slugrustle/electronics/Big_Fast_Switch/Simulation/Diode_SPICE_Models.pdf

3.13. OTHER DIODE TECHNOLOGIES | 163

or laser diode’s optimum forward current. This is especially important for the laser diode, not so much for the LED, as regular LEDs tend to be more tolerant of forward current variations. Another application is in the charging of small secondary-cell batteries, where a constant charging current leads to predictable charging times. Of course, large secondary-cell battery banks might also benefit from constant-current charging, but constant-current diodes tend to be very small devices, limited to regulating currents in the milliamp range.

## 3.13 Other diode technologies

### 3.13.1 SiC diodes

Diodes manufactured from silicon carbide are capable of high temperature operation to 400oC. This could be in a high temperature environment: down hole oil well logging, gas turbine engines, auto engines. Or, operation in a moderate environment at high power dissipation. Nuclear and space applications are promising as SiC is 100 times more resistant to radiation compared with silicon. SiC is a better conductor of heat than any metal. Thus, SiC is better than silicon at conducting away heat. Breakdown voltage is several kV. SiC power devices are expected to reduce electrical energy losses in the power industry by a factor of 100.

### 3.13.2 Polymer diode

Diodes based on organic chemicals have been produced using low temperature processes. Hole rich and electron rich conductive polymers may be ink jet printed in layers. Most of the research and development is of the organic LED (OLED). However, development of inexpensive printable organic RFID (radio frequency identification) tags is on going. In this effort, a pentacene organic rectifier has been operated at 50 MHz. Rectification to 800 MHz is a development goal. An inexpensive metal insulator metal (MIM) diode acting like a back-to-back zener diode clipper has been delveloped. Also, a tunnel diode like device has been fabricated.

## 3.14 SPICE models

The SPICE circuit simulation program provides for modeling diodes in circuit simulations. The diode model is based on characterization of individual devices as described in a product data sheet and manufacturing process characteristics not listed. Some information has been extracted from a 1N4004 data sheet in Figure 3.86.
The diode statement begins with a diode element name which must begin with “d” plus optional characters. Example diode element names include: d1, d2, dtest, da, db, d101. Two node numbers specify the connection of the anode and cathode, respectively, to other components. The node numbers are followed by a model name, referring to a subsequent “.model” statement.
The model statement line begins with “.model,” followed by the model name matching one or more diode statements. Next, a “d” indicates a diode is being modeled. The remainder of the model statement is a list of optional diode parameters of the form Parameter-

164 CHAPTER 3. DIODES AND RECTIFIERS

1

10

100

1 | 10 | 100

1.0

10

0.6 | 1.6

0.01

0.1

0.8 1.0 1.2 1.4
VF

instaneous forward voltage (V)

### IF instaneous forward current (I)

VR reverse voltage (V)

### CJ junction capacitance (pF)

30

0.925

Max avg rectified current IO (A) 1 Peak repetitive reverse voltage VRRM (V) 400 Peak forward surge current IFSM (A) 30

Forward voltage drop VF

(V) 1
@ IF
(A) 1
Max reverse current IR (µΑ) 5 Total capacitance CT
(pF) 15 | @ VR (V) 400

Figure 3.86: Data sheet 1N4004 excerpt, after [6].

Name=ParameterValue. None are used in Example below. Example2 has some parameters defined. For a list of diode parameters, see Table 3.6.

General form: d[name] [anode] [cathode] [modelname]
.model ([modelname] d [parmtr1=x] [parmtr2=y] . . .)
Example: | d1 1 2 mod1
.model mod1 d
Example2: | D2 1 2 Da1N4004
.model Da1N4004 D (IS=18.8n RS=0 BV=400 IBV=5.00u CJO=30 M=0.333 N=2)

The easiest approach to take for a SPICE model is the same as for a data sheet: consult the manufacturer’s web site. Table 3.7 lists the model parameters for some selected diodes. A fallback strategy is to build a SPICE model from those parameters listed on the data sheet. A third strategy, not considered here, is to take measurements of an actual device. Then, calculate, compare and adjust the SPICE parameters to the measurements.
If diode parameters are not specified as in “Example” model above, the parameters take on the default values listed in Table 3.6 and Table 3.7. These defaults model integrated circuit diodes. These are certainly adequate for preliminary work with discrete devices For more critical work, use SPICE models supplied by the manufacturer [5], SPICE vendors, and other

3.14. SPICE MODELS | 165

Table 3.6: Diode SPICE parameters
Symbol | Name | Parameter | Units | Default
IS | IS | Saturation current (diode equa-
| | tion)

A 1E-14

RS | RS | Parsitic resistance (series resis-
| | tance) | Ω | 0
n | N | Emission coefficient, 1 to 2 | - | 1
τ D | TT | Transit time | s | 0
CD(0) | CJO | Zero-bias junction capacitance | F | 0
φ0 | VJ | Junction potential | V | 1
m | M | Junction grading coefficient | - | 0.5
- | - | 0.33 for linearly graded junc-
| | tion
- | - | 0.5 for abrupt junction | - | -
Eg | EG | Activation energy: | eV | 1.11
- | - | Si: 1.11 | - | -
- | - | Ge: 0.67 | - | -
- | - | Schottky: 0.69 | - | -
pi | XTI | IS temperature exponent | - | 3.0
- | - | pn junction: 3.0 | - | -
- | - | Schottky: 2.0 | - | -
kf | KF | Flicker noise coefficient | - | 0
af | AF | Flicker noise exponent | - | 1
FC | FC | Forward bias depletion capaci-
| | tance coefficient
- 0.5
BV | BV | Reverse breakdown voltage | V | ∞
IBV | IBV | Reverse breakdown current | A | 1E-3

166 CHAPTER 3. DIODES AND RECTIFIERS

sources. [16]

Table 3.7: SPICE parameters for selected diodes; sk=schottky Ge=germanium; else silicon.
Part | IS | RS | N | TT | CJO | M | VJ | EG | XTI | BV | IBV
Default 1N5711 sk 1N5712 sk 1N34 Ge 1N4148 1N3891 10A04 10A 1N4004 1A 1N4004 data sheet | 1E-14 315n 680p 200p 35p 63n 844n 76.9n 18.8n | 0 2.8 12 84m 64m 9.6m 2.06m 42.2m - | 1 2.03 1.003 2.19 1.24 2 2.06 1.45 2 | 0 1.44n 50p 144n 5.0n 110n 4.32u 4.32u - | 0 2.00p 1.0p 4.82p 4.0p 114p 277p 39.8p 30p | 0.5 0.333 0.5 0.333 0.285 0.255 0.333 0.333 0.333 | 1 -0.6 0.75 0.6 0.6 --- | 1.11 0.69 0.69 0.67 ----- | 3 2 2 ------ | ∞ 70 20 60 75 250 400 400 400 | 1m 10u -15u --10u 5u 5u

Otherwise, derive some of the parameters from the data sheet. First select a value for spice parameter N between 1 and 2. It is required for the diode equation (n). Massobrio [1] pp 9, recommends ”.. n, the emission coefficient is usually about 2.” In Table 3.7, we see that power rectifiers 1N3891 (12 A), and 10A04 (10 A) both use about 2. The first four in the table are not relevant because they are schottky, schottky, germanium, and silicon small signal, respectively. The saturation current, IS, is derived from the diode equation, a value of (VD, ID) on the graph in Figure 3.86, and N=2 (n in the diode equation).

ID = IS(e

VD/nVT − 1)

VT = 26 mV at 25oC | n = 2.0 | VD = 0.925 V at 1 A from graph

1 A = IS(e

(0.925V )/(2)(26mV ) − 1)

IS = 18.8E-9

The numerical values of IS=18.8n and N=2 are entered in last line of Table 3.7 for comparison to the manufacturers model for 1N4004, which is considerably different. RS defaults to 0 for now. It will be estimated later. The important DC static parameters are N, IS, and RS. Rashid [15] suggests that TT, τ D, the transit time, be approximated from the reverse recovery stored charge QRR, a data sheet parameter (not available on our data sheet) and IF , forward current.

ID = IS(e

VD/nVT − 1)

τ D = QRR/IF

We take the TT=0 default for lack of QRR. Though it would be reasonable to take TT for a similar rectifier like the 10A04 at 4.32u. The 1N3891 TT is not a valid choice because it is a

3.14. SPICE MODELS | 167

fast recovery rectifier. CJO, the zero bias junction capacitance is estimated from the VR vs CJ graph in Figure 3.86. The capacitance at the nearest to zero voltage on the graph is 30 pF at 1 V. If simulating high speed transient response, as in switching regulator power supplies, TT and CJO parameters must be provided.
The junction grading coefficient M is related to the doping profile of the junction. This is not a data sheet item. The default is 0.5 for an abrupt junction. We opt for M=0.333 corresponding to a linearly graded junction. The power rectifiers in Table 3.7 use lower values for M than 0.5. We take the default values for VJ and EG. Many more diodes use VJ=0.6 than shown in Table 3.7. However the 10A04 rectifier uses the default, which we use for our 1N4004 model (Da1N4001 in Table 3.6). Use the default EG=1.11 for silicon diodes and rectifiers. Table 3.6 lists values for schottky and germanium diodes. Take the XTI=3, the default IS temperature coefficient for silicon devices. See Table 3.6 for XTI for schottky diodes.
The abbreviated data sheet, Figure 3.86, lists IR = 5 µA @ VR = 400 V, corresponding to IBV=5u and BV=400 respectively. The 1n4004 SPICE parameters derived from the data sheet are listed in the last line of Table 3.7 for comparison to the manufacturer’s model listed above it. BV is only necessary if the simulation exceeds the reverse breakdown voltage of the diode, as is the case for zener diodes. IBV, reverse breakdown current, is frequently omitted, but may be entered if provided with BV.
Figure 3.87 shows a circuit to compare the manufacturers model, the model derived from the datasheet, and the default model using default parameters. The three dummy 0 V sources are necessary for diode current measurement. The 1 V source is swept from 0 to 1.4 V in 0.2 mV steps. See .DC statement in the netlist in Table 3.8. DI1N4004 is the manufacturer’s diode model, Da1N4004 is our derived diode model.

0

+
− 1V

D1 D2 1

0V −

0V −

0V −

D3

Figure 3.87: SPICE circuit for comparison of manufacturer model (D1), calculated datasheet model (D2), and default model (D3).

We compare the three models in Figure 3.88. and to the datasheet graph data in Table 3.9. VD is the diode voltage versus the diode currents for the manufacturer’s model, our calculated datasheet model and the default diode model. The last column “1N4004 graph” is from the datasheet voltage versus current curve in Figure 3.86 which we attempt to match. Comparison of the currents for the three model to the last column shows that the default model is good at low currents, the manufacturer’s model is good at high currents, and our calculated datasheet model is best of all up to 1 A. Agreement is almost perfect at 1 A because the IS calculation is based on diode voltage at 1 A. Our model grossly over states current above 1 A.
The solution is to increase RS from the default RS=0. Changing RS from 0 to 8m in the datasheet model causes the curve to intersect 10 A (not shown) at the same voltage as the manufacturer’s model. Increasing RS to 28.6m shifts the curve further to the right as shown in

168 CHAPTER 3. DIODES AND RECTIFIERS

Table 3.8: SPICE netlist parameters: (D1) DI1N4004 manufacturer’s model, (D2) Da1N40004 datasheet derived, (D3) default diode model.
*SPICE circuit <03468.eps> from XCircuit v3.20
D1 1 5 DI1N4004
V1 5 0 0
D2 1 3 Da1N4004
V2 3 0 0
D3 1 4 Default
V3 4 0 0
V4 1 0 1
.DC V4 0 1400mV 0.2m
.model Da1N4004 D (IS=18.8n RS=0 | BV=400 IBV=5.00u CJO=30
+M=0.333 | N=2.0 TT=0)
.MODEL DI1N4004 D (IS=76.9n RS=42.0m BV=400 IBV=5.00u CJO=39.8p +M=0.333 N=1.45 TT=4.32u)
.MODEL Default D
.end

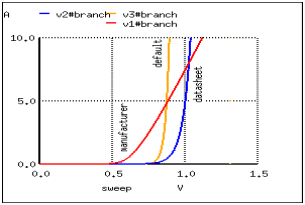
[picture p3: figure]

Figure 3.88: First trial of manufacturer model, calculated datasheet model, and default model.

3.14. SPICE MODELS | 169

Table 3.9: Comparison of manufacturer model, calculated datasheet model, and default model to 1N4004 datasheet graph of V vs I.

| | model | model | model
1N4004
index | VD | manufacturer | datasheet | default
graph
3500 | 7.000000e-01 | 1.612924e+00 | 1.416211e-02 | 5.674683e-03
0.01
4001 | 8.002000e-01 | 3.346832e+00 | 9.825960e-02 | 2.731709e-01
0.13
4500 | 9.000000e-01 | 5.310740e+00 | 6.764928e-01 | 1.294824e+01
0.7
4625 | 9.250000e-01 | 5.823654e+00 | 1.096870e+00 | 3.404037e+01
1.0
5000 | 1.000000e-00 | 7.395953e+00 | 4.675526e+00 | 6.185078e+02
2.0
5500 | 1.100000e+00 | 9.548779e+00 | 3.231452e+01 | 2.954471e+04
3.3
6000 | 1.200000e+00 | 1.174489e+01 | 2.233392e+02 | 1.411283e+06
5.3
6500 | 1.300000e+00 | 1.397087e+01 | 1.543591e+03 | 6.741379e+07
8.0
7000 | 1.400000e+00 | 1.621861e+01 | 1.066840e+04 | 3.220203e+09 12.

170 CHAPTER 3. DIODES AND RECTIFIERS

Figure 3.89. This has the effect of more closely matching our datasheet model to the datasheet graph (Figure 3.86). Table 3.10 shows that the current 1.224470e+01 A at 1.4 V matches the graph at 12 A. However, the current at 0.925 V has degraded from 1.096870e+00 above to 7.318536e-01.

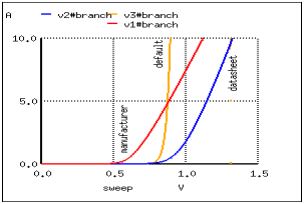
[picture p4: figure]

Figure 3.89: Second trial to improve calculated datasheet model compared with manufacturer model and default model.

Table 3.10: Changing Da1N4004 model statement RS=0 to RS=28.6m decreases the current at VD=1.4 V to 12.2 A.
.model Da1N4004 D (IS=18.8n RS=28.6m BV=400 IBV=5.00u CJO=30
+M=0.333 | N=2.0 TT=0)
| | model | model | 1N4001
index | VD | manufacturer | datasheet | graph
3505 | 7.010000e-01 | 1.628276e+00 | 1.432463e-02 | 0.01
4000 | 8.000000e-01 | 3.343072e+00 | 9.297594e-02 | 0.13
4500 | 9.000000e-01 | 5.310740e+00 | 5.102139e-01 | 0.7
4625 | 9.250000e-01 | 5.823654e+00 | 7.318536e-01 | 1.0
5000 | 1.000000e-00 | 7.395953e+00 | 1.763520e+00 | 2.0
5500 | 1.100000e+00 | 9.548779e+00 | 3.848553e+00 | 3.3
6000 | 1.200000e+00 | 1.174489e+01 | 6.419621e+00 | 5.3
6500 | 1.300000e+00 | 1.397087e+01 | 9.254581e+00 | 8.0
7000 | 1.400000e+00 | 1.621861e+01 | 1.224470e+01 | 12.

Suggested reader exercise: decrease N so that the current at VD=0.925 V is restored to 1
A. This may increase the current (12.2 A) at VD=1.4 V requiring an increase of RS to decrease current to 12 A.

3.14. SPICE MODELS | 171

Zener diode: There are two approaches to modeling a zener diode: set the BV parameter to the zener voltage in the model statement, or model the zener with a subcircuit containing a diode clamper set to the zener voltage. An example of the first approach sets the breakdown voltage BV to 15 for the 1n4469 15 V zener diode model (IBV optional):

.model D1N4469 D ( BV=15 IBV=17m )

The second approach models the zener with a subcircuit. Clamper D1 and VZ in Figure ?? models the 15 V reverse breakdown voltage of a 1N4477A zener diode. Diode DR accounts for the forward conduction of the zener in the subcircuit.

+

−
13.7 V

1
3

2

A

K

D1

.SUBCKT DI-1N4744A
1 2
* Terminals A K
D1 1 2 DF
DZ 3 1 DR
VZ 2 3 13.7
.MODEL DF D (
IS=27.5p RS=0.620
N=1.10
+ CJO=78.3p
VJ=1.00 M=0.330
TT=50.1n )
.MODEL DR D (
IS=5.49f RS=0.804
N=1.77 )
.ENDS

Figure 3.90: Zener diode subcircuit uses clamper (D1 and VZ) to model zener.

Tunnel diode: A tunnel diode may be modeled by a pair of field effect transistors (JFET) in a SPICE subcircuit. [11] An oscillator circuit is also shown in this reference.
Gunn diode: A Gunn diode may also be modeled by a pair of JFET’s. [12] This reference shows a microwave relaxation oscillator.
- REVIEW:
- Diodes are described in SPICE by a diode component statement referring to .model statement. The .model statement contains parameters describing the diode. If parameters are not provided, the model takes on default values.
- Static DC parameters include N, IS, and RS. Reverse breakdown parameters: BV, IBV.
- Accurate dynamic timing requires TT and CJO parameters
- Models provided by the manufacturer are highly recommended.
