slugrustle/electronics/Big_Fast_Switch/MOSFET_and_NTC_Heatsink_Mounting.jpg

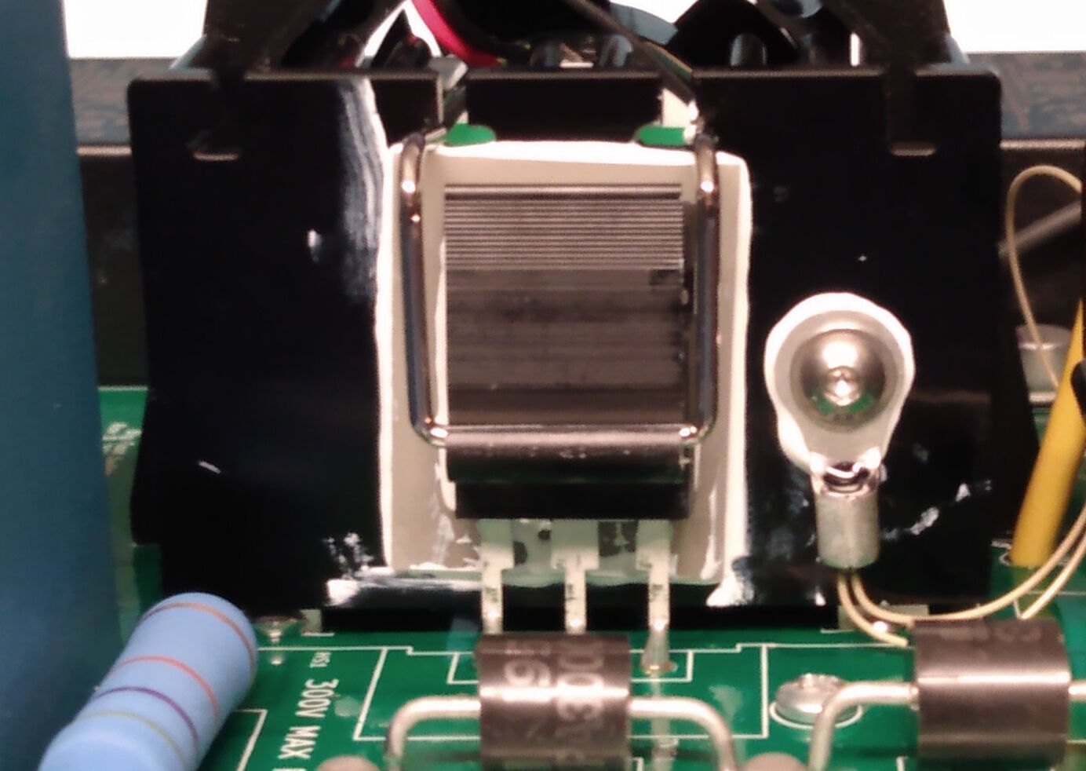
Big_Fast_Switch/MOSFET_and_NTC_Heatsink_Mounting.jpg
