slugrustle/electronics/HighImpedanceBuffer/Enclosure/BufferBoxLid_DiagonalView.png

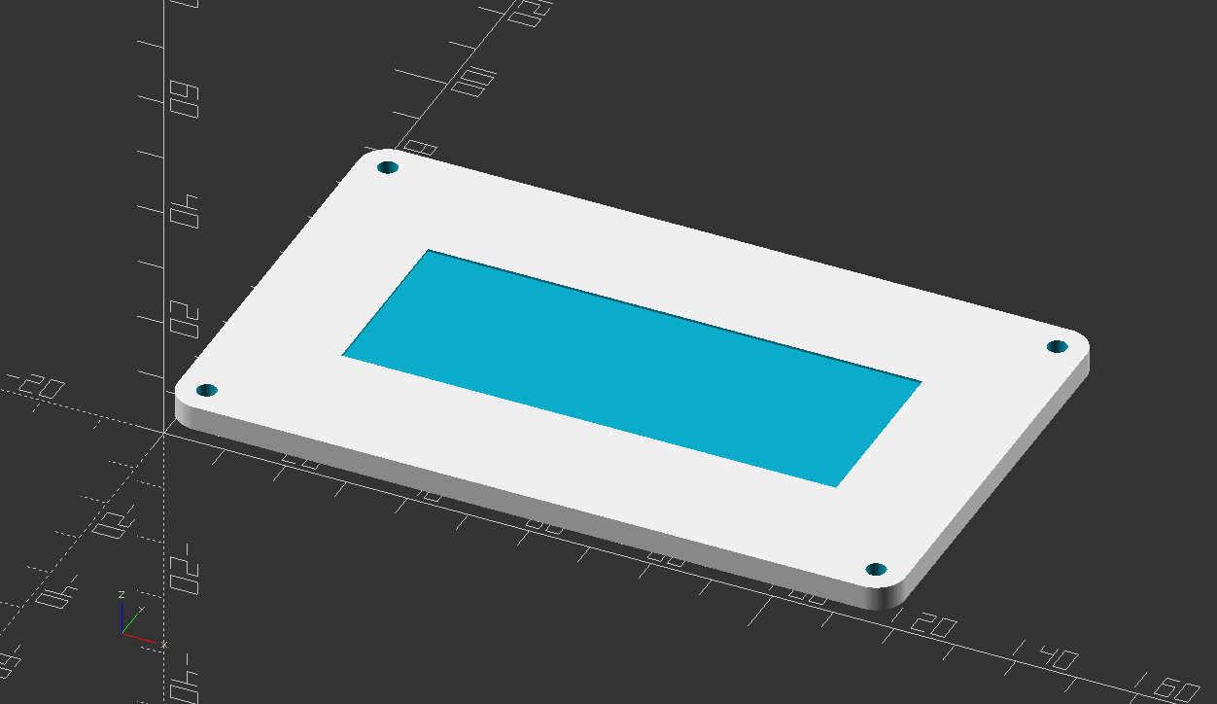
HighImpedanceBuffer/Enclosure/BufferBoxLid_DiagonalView.png
