slugrustle/electronics/HighImpedanceBuffer/Bill_of_Materials/HighImpedanceBuffer_BoM.pdf

High Impedance Buffer Rev4 Bill of Materials
2019-10-01
Part # | Quantity | Designators | Manufacturer | Description
PJ-102AH | 1 | J1 | CUI Inc. | Jack for 2.1mm ID, 5.5mm OD barrel plug
WAU20-200 | 1 | — | Triad Magnetics | 120VAC 60Hz input, 20VAC 200mA output wall adapter. 2.1mm ID, 5.5mm OD barrel plug
SF-2410FP0375T-2 | 1 | F1 | Bourns | 375mA 125V 0.1502A² s fast fuse, 2410 case
SMBJ36CA-13-F | 1 | D3 | Diodes Inc. | 36V VWM bidirectional TVS diode, SMB case
NRVTSA4100ET3G | 2 | D4, D5 | ON Semiconductor | 100V low leakage, low VF Schottky diode, SMA case
EEV-TG1H471M | 2 | C5, C6 | Panasonic | 470µF, 50V, 125°C, low ESR electrolytic capacitor
CKG57NX7R2A106M500JH | 4 | C3, C4, C9, C10 | TDK | 10µF, 100V, X7R, dual stacked J-Lead capacitor
SMBJ18A | 2 | D1, D2 | Taiwan Semicon-ductor | 18V VWM unidirectional TVS diode, SMB case
TPS7A4901DGNR | 1 | U1 | Texas Instruments | 36V linear regulator, 8-MSOP-EP
TPS7A3001DGNR | 1 | U2 | Texas Instruments | 36V negative linear regula-tor, 8-MSOP-EP
GRM1885C1H103JA01D | 4 | C1, C2, C7, C8 | Murata Electronics | 10nF 50V NP0 capacitor, 0603 case
DPAD1 | 4 | D6–D9 | Linear Systems | Dual 45V picoamp diode, TO-78-5L case
CC0805KRX7R9BB104 | 4 | C13–C16 | Yageo | 100nF 50V X7R capacitor, 0805 case
CL31B105KBHNNNE | 4 | C11, C12, C17, C18 | Samsung Electro-Mechanics | 1µF 50V X7R capacitor, 1206 case
TBD | 2 | C19, C20 | TBD | TBDpF ±5% 50V NP0 ca-pacitor, 0603 case
OPA192IDR | 2 | U3, U4 | Texas Instruments | ±18V low offset, low bias current, high input impedance rail-to-rail op amp

1 / 2

Part # | Quantity | Designators | Manufacturer | Description
CMDD6001 | 4 | D10–D13 | Central Semicon-ductor | 75V Low leakage diode, SOD323 case
MMBZ27VAL,215 | 2 | D14, D15 | Nexperia | Dual (common anode) low leakage 22V VWM TVS diode, SOT23-3 case
1776540 | 1 | J2 | Phoenix Contact | 6 position, 5.08mm pitch right angle socket for ter-minal block plug
1778027 | 1 | — | Phoenix Contact | 6 position 5.08mm pitch terminal block plug, screw clamp
ERA-3ARB622V | 2 | R1, R2 | Panasonic | 6.2kΩ ±0.1% ±10ppm/°C 0.1W resistor, 0603 case
RQ73C1J88K7BTD | 2 | R3, R4 | TE Connectivity | 88.7kΩ ±0.1% ±10ppm/°C 0.1W resistor, 0603 case
RC1206JR-072R2L | 2 | R5, R6 | Yageo | 2.2Ω ±5% ±200ppm/°C 0.25W resistor, 1206 case
RC1206FR-0710KL | 2 | R7, R8 | Yageo | 10kΩ ±1% ±100ppm/°C 0.25W resistor, 1206 case
RC1206FR-072K7L | 2 | R11, R13 | Yageo | 2.7kΩ ±1% ±100ppm/°C 0.25W resistor, 1206 case
RC0805FR-071KL | 4 | R9, R10, R12, R14 | Yageo | 1kΩ ±1% ±100ppm/°C 0.125W resistor, 0805 case
RC0805FR-0720RL | 2 | R15, R16 | Yageo | 20Ω ±1% ±100ppm/°C 0.125W resistor, 0805 case
RC1206FR-07100RL | 2 | R17, R18 | Yageo | 100Ω ±1% ±100ppm/°C 0.25W resistor, 1206 case
90380A008 | 6 | S1–S6 | McMaster-Carr | #2-28 thread, 0.3125” long shank, 0.167” head diam-eter thread forming screw for plastics
94997A125 | 2 | — | McMaster-Carr | M2.2 x 6.5c thread forming screw
93365A122 | 4 | — | McMaster-Carr | #4-40 heat set threaded in-sert for plastic, 0.219” tall
90272A107 | 4 | — | McMaster-Carr | #4-40 thread, 0.3125” long shank machine screw

2 / 2
