slugrustle/electronics/SOT23ZenerTester/SupportPlate/SOT23ZenerTester_Plate_DiagonalView.png

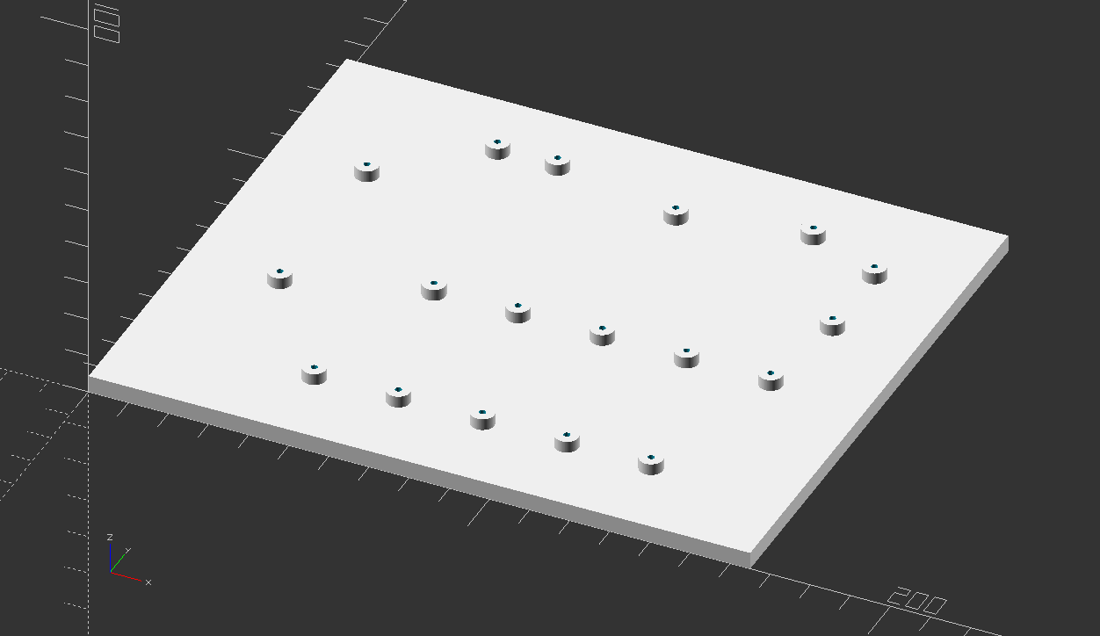
SOT23ZenerTester/SupportPlate/SOT23ZenerTester_Plate_DiagonalView.png
