slugrustle/electronics/TestSequencer/Enclosure/TestSequencer_BottomPlate_DiagonalView.png

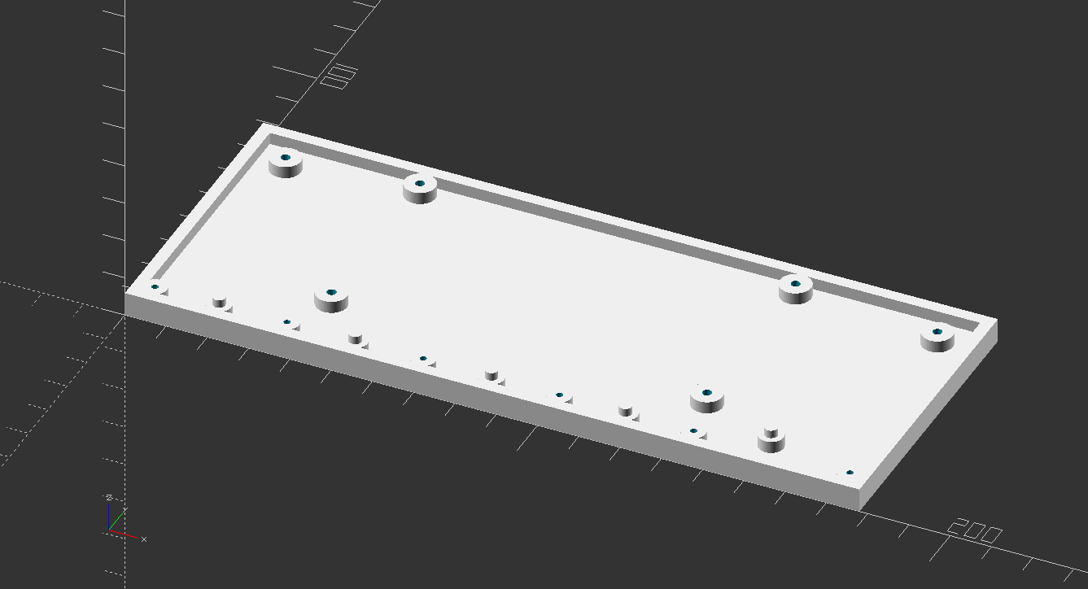
TestSequencer/Enclosure/TestSequencer_BottomPlate_DiagonalView.png
