slugrustle/electronics/TestSequencer/Enclosure/TestSequencer_TopCover_DiagonalView.png

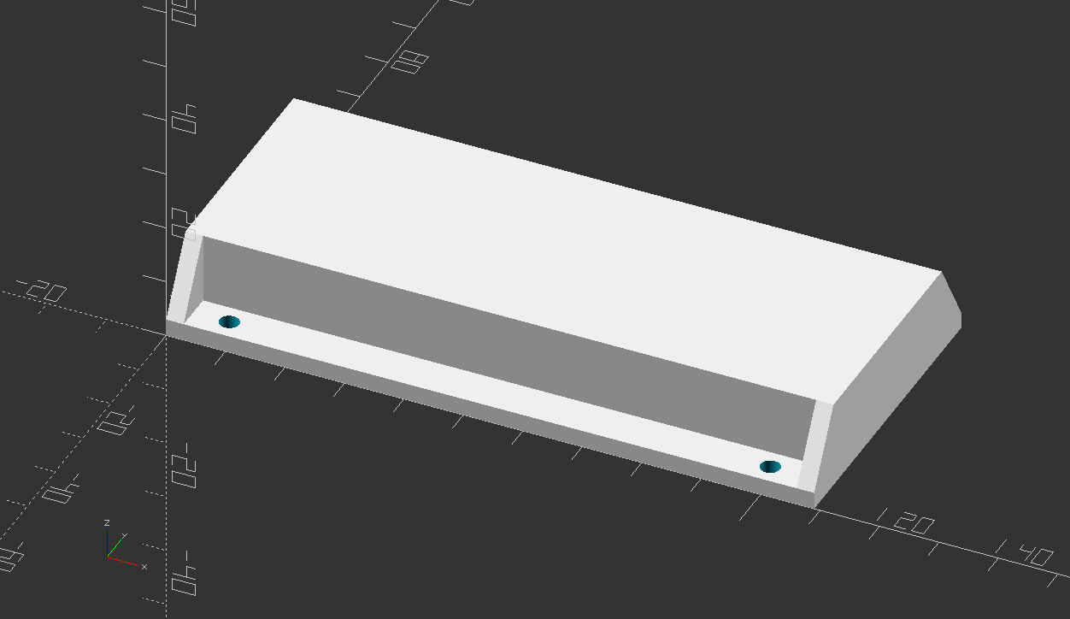
TestSequencer/Enclosure/TestSequencer_TopCover_DiagonalView.png
