slugrustle/electronics/Big_Fast_Switch/Simulation/LED_test.asc

D1: LED; APT2012SURCK
V1: voltage; 0
Named nets: 0, Vf
.MODEL APT2012SURCK D (IS=4.291886e-17 RS=2.353504 N=2.186609 EG=1.405 CJO=35p BV=5 IBV=10u )
.TEMP 25
.dc V1 0 2 1m
